christopherrbrown3/roanoke-star-tree-topper/pentagrammic_prism/previews/front.png

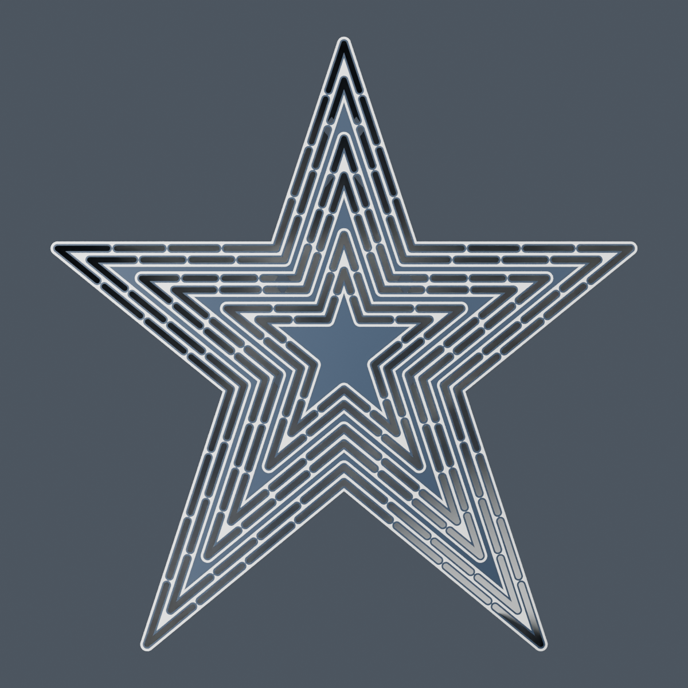
pentagrammic_prism/previews/front.png
