christopherrbrown3/roanoke-star-tree-topper/pentagrammic_prism/previews/rear.png

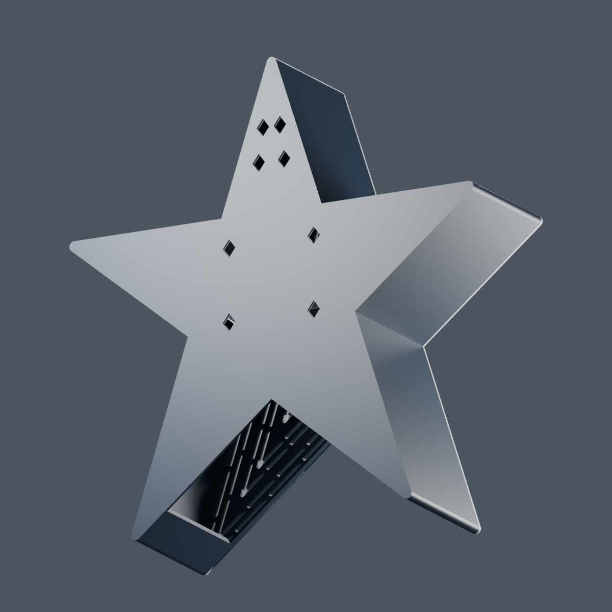
pentagrammic_prism/previews/rear.png
