christopherrbrown3/roanoke-star-tree-topper/print_in_place/body_material.stl

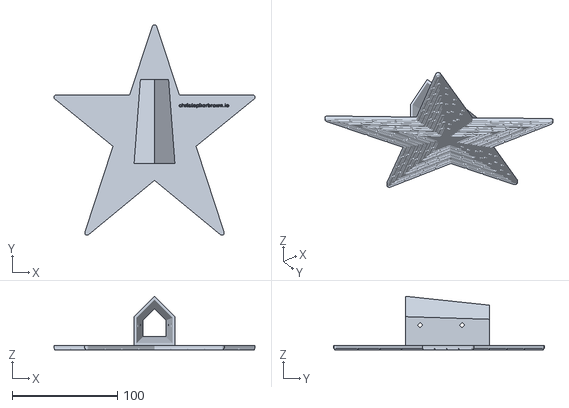
[picture p39: CAD file, 2026-09-19]
print_in_place/body_material.stl
191.0 x 200.0 x 50.8
