christopherrbrown3/roanoke-star-tree-topper/snap_back_prism/connector_fit_v2/construction/two_dot_wall.stl

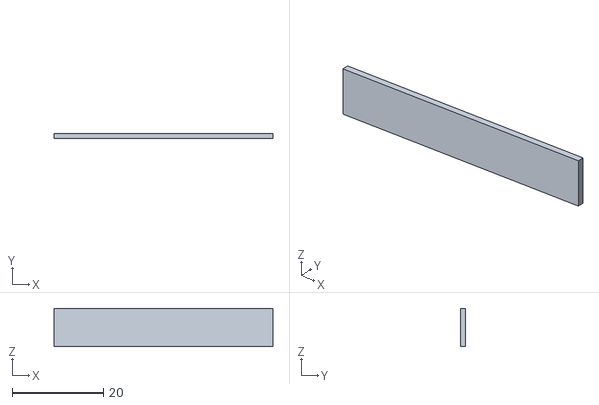
[picture p40: CAD file, 2026-10-10]
snap_back_prism/connector_fit_v2/construction/two_dot_wall.stl
48.0 x 1.20 x 8.40
