christopherrbrown3/roanoke-star-tree-topper/snap_back_prism/connector_fit_v2/two_dot_back.stl

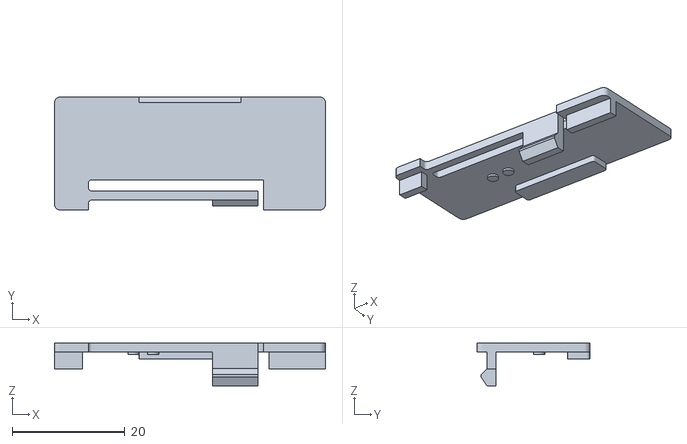
[picture p41: CAD file, 2026-10-10]
snap_back_prism/connector_fit_v2/two_dot_back.stl
48.0 x 20.0 x 7.60
