christopherrbrown3/roanoke-star-tree-topper/snap_back_prism/connector_sample_A1.3mf

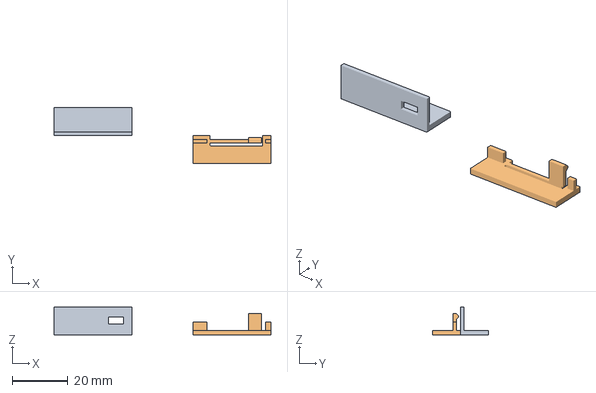
[picture p42: CAD file, 2026-10-10]
snap_back_prism/connector_sample_A1.3mf
78.0 x 20.0 x 9.90 mm
Snap connector sample x 2
