christopherrbrown3/roanoke-star-tree-topper/snap_back_prism/construction/hook_2.stl

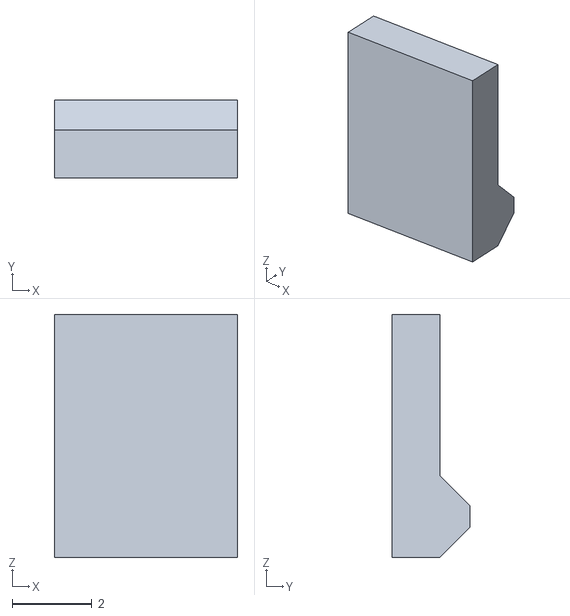
[picture p43: CAD file, 2026-10-10]
snap_back_prism/construction/hook_2.stl
4.60 x 1.95 x 6.10
