christopherrbrown3/roanoke-star-tree-topper/snap_back_prism/diffused/body_black.stl

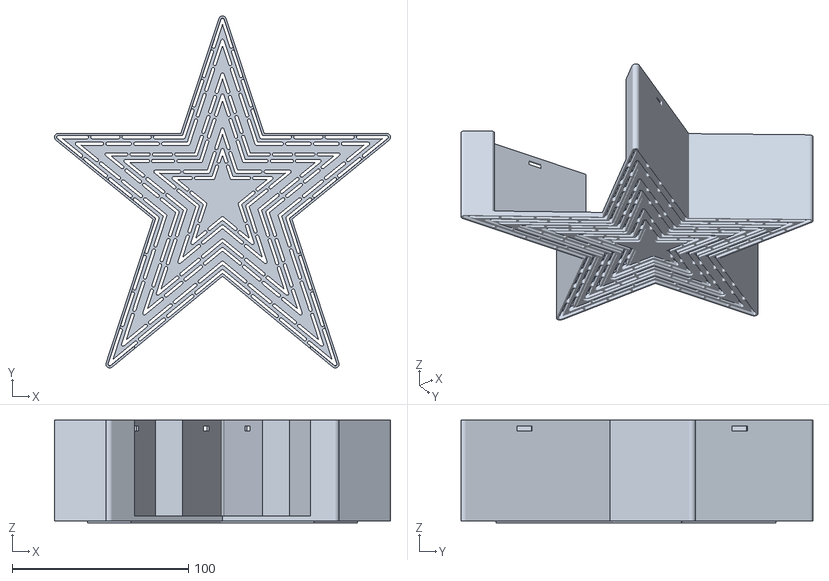
[picture p44: CAD file, 2026-10-10]
snap_back_prism/diffused/body_black.stl
191.0 x 200.0 x 58.4
