christopherrbrown3/roanoke-star-tree-topper/snap_back_prism/diffused/construction/white_upper_bands.stl

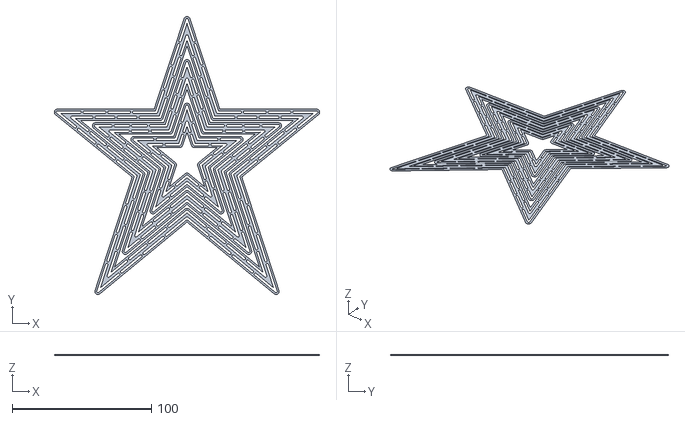
[picture p45: CAD file, 2026-10-10]
snap_back_prism/diffused/construction/white_upper_bands.stl
191.0 x 200.0 x 0.6
