christopherrbrown3/roanoke-star-tree-topper/snap_back_prism/two_dot/body_white_face.stl

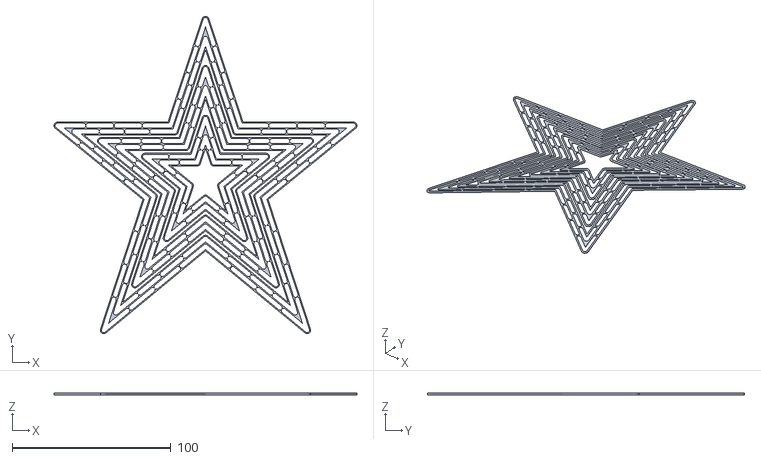
[picture p46: CAD file, 2026-10-10]
snap_back_prism/two_dot/body_white_face.stl
191.0 x 200.0 x 1.00
