christopherrbrown3/roanoke-star-tree-topper/snap_back_prism/two_dot/construction/hook_5.stl

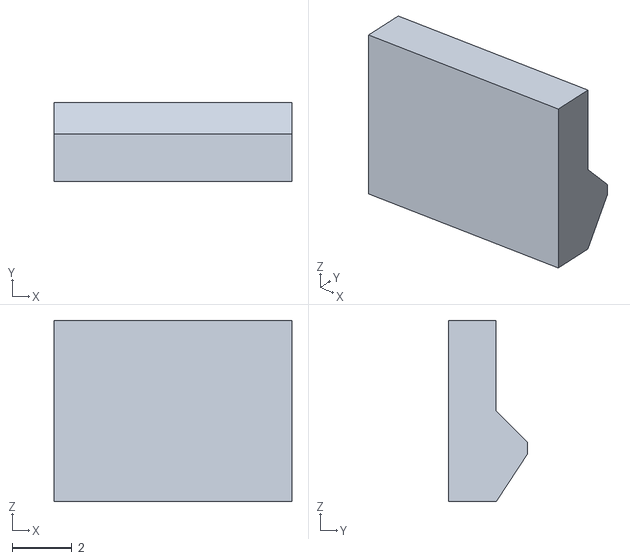
[picture p47: CAD file, 2026-10-10]
snap_back_prism/two_dot/construction/hook_5.stl
8.00 x 2.65 x 6.10
