christopherrbrown3/roanoke-star-tree-topper/pentagrammic_prism/roanoke_star_prism.stl

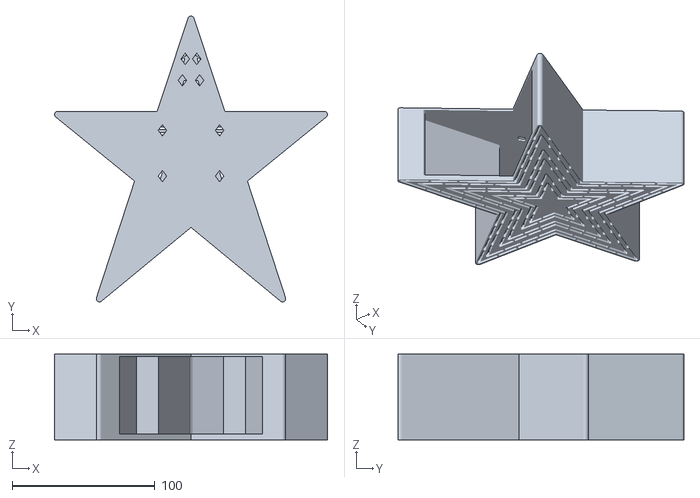
[picture p48: CAD file, 2026-10-10]
pentagrammic_prism/roanoke_star_prism.stl
191.0 x 200.0 x 60.0
