christopherrbrown3/roanoke-star-tree-topper/print_in_place/roanoke_star_A1_geometry_reference.stl

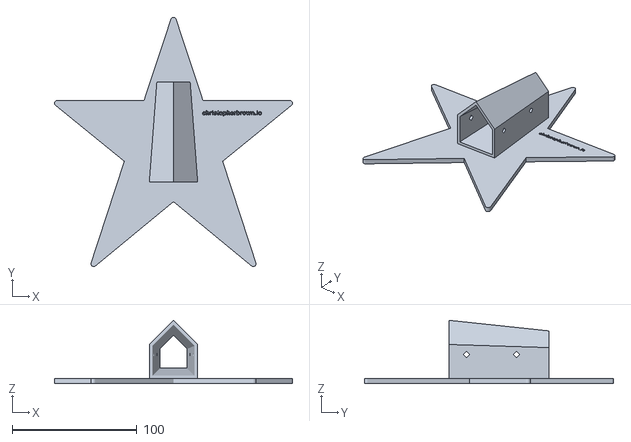
[picture p49: CAD file, 2026-09-19]
print_in_place/roanoke_star_A1_geometry_reference.stl
191.0 x 200.0 x 50.8
