christopherrbrown3/roanoke-star-tree-topper/snap_back_prism/construction/hook_1.stl

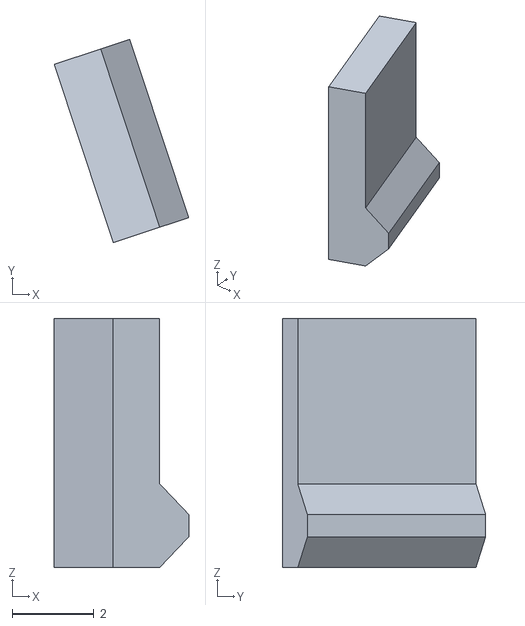
[picture p50: CAD file, 2026-10-10]
snap_back_prism/construction/hook_1.stl
3.30 x 4.98 x 6.10
