christopherrbrown3/roanoke-star-tree-topper/snap_back_prism/coupon_back.stl

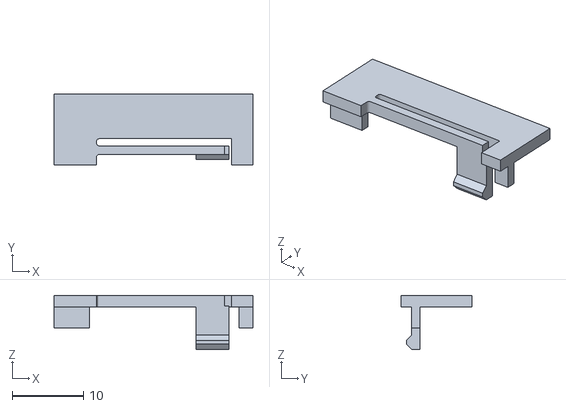
[picture p51: CAD file, 2026-10-10]
snap_back_prism/coupon_back.stl
28.0 x 10.0 x 7.60
