christopherrbrown3/roanoke-star-tree-topper/snap_back_prism/diffused/construction/continuous_white_face_region.stl

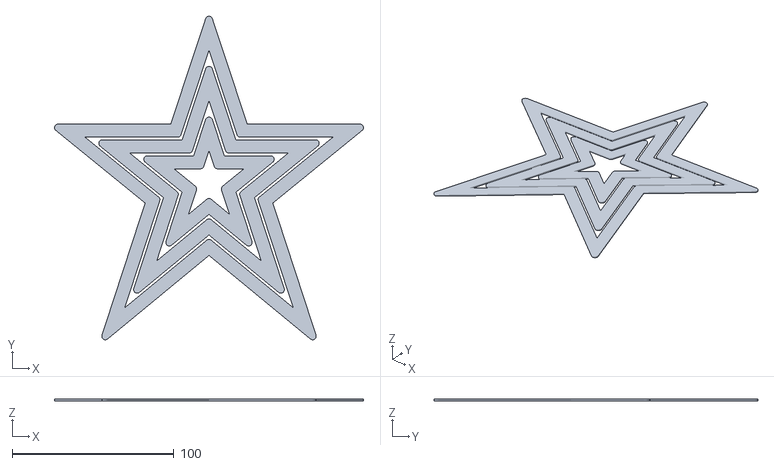
[picture p52: CAD file, 2026-10-10]
snap_back_prism/diffused/construction/continuous_white_face_region.stl
191.0 x 200.0 x 1.00
