christopherrbrown3/roanoke-star-tree-topper/snap_back_prism/spacing_v3/body_white_diffused.stl

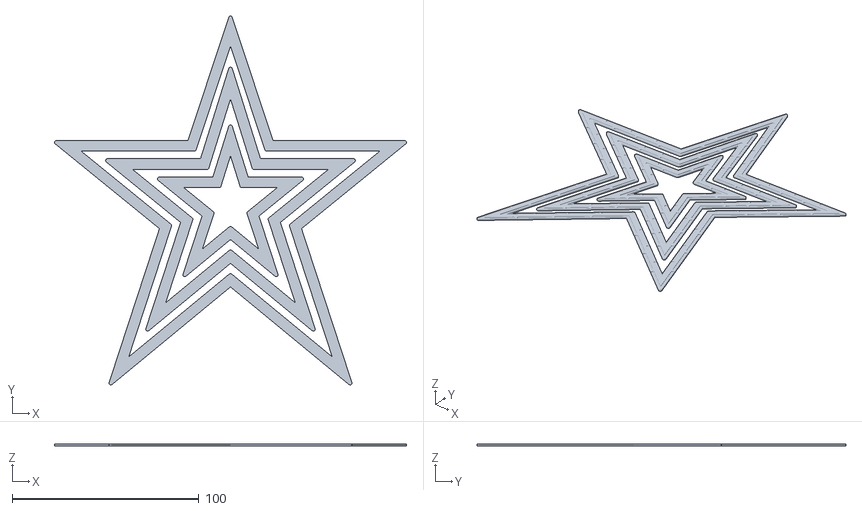
[picture p53: CAD file, 2026-10-10]
snap_back_prism/spacing_v3/body_white_diffused.stl
188.6 x 197.6 x 1.00
