christopherrbrown3/roanoke-star-tree-topper/snap_back_prism/two_dot/construction/lid_blank.stl

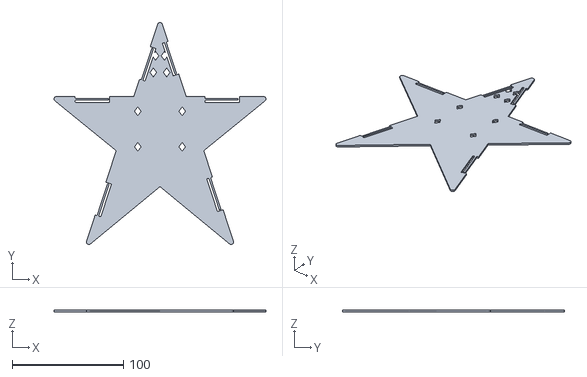
[picture p54: CAD file, 2026-10-10]
snap_back_prism/two_dot/construction/lid_blank.stl
191.0 x 200.0 x 1.60
