christopherrbrown3/roanoke-star-tree-topper/pentagrammic_prism/construction/bottom_mouth.stl

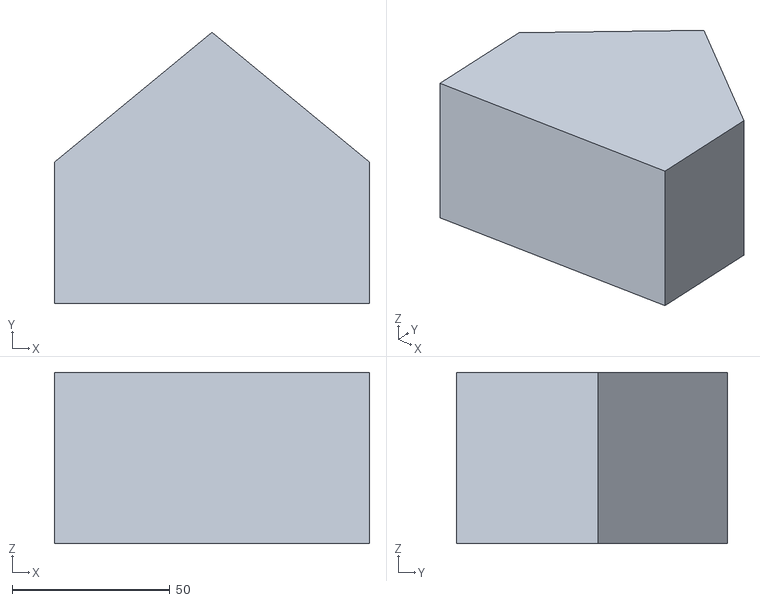
[picture p55: CAD file, 2026-10-10]
pentagrammic_prism/construction/bottom_mouth.stl
100.0 x 86.1 x 54.4
