christopherrbrown3/roanoke-star-tree-topper/pentagrammic_prism/dark_shell.stl

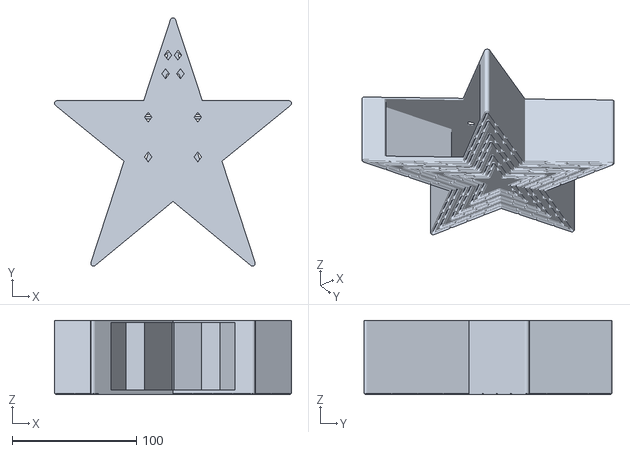
[picture p56: CAD file, 2026-10-10]
pentagrammic_prism/dark_shell.stl
191.0 x 200.0 x 60.0
