christopherrbrown3/roanoke-star-tree-topper/print_in_place/white_tube_material.stl

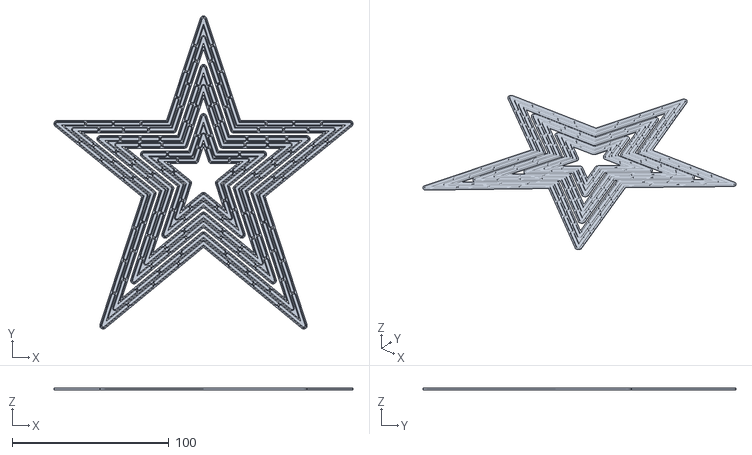
[picture p57: CAD file, 2026-09-19]
print_in_place/white_tube_material.stl
191.0 x 200.0 x 1.00
