christopherrbrown3/roanoke-star-tree-topper/snap_back_prism/connector_fit_v2/connector_fit_v2_A1.3mf

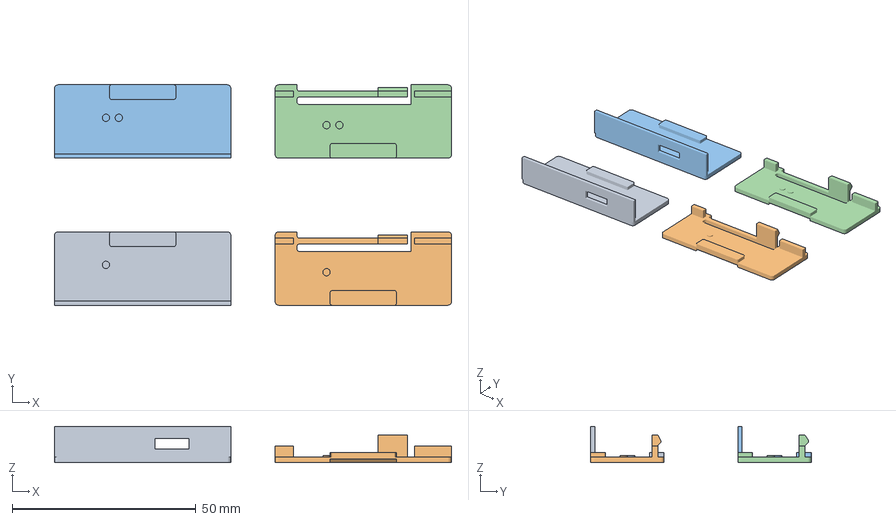
[picture p58: CAD file, 2026-10-10]
snap_back_prism/connector_fit_v2/connector_fit_v2_A1.3mf
108.0 x 60.0 x 9.90 mm
Connector fit v2 - one and two dots x 4
