christopherrbrown3/roanoke-star-tree-topper/snap_back_prism/connector_fit_v2/construction/two_dot_floor.stl

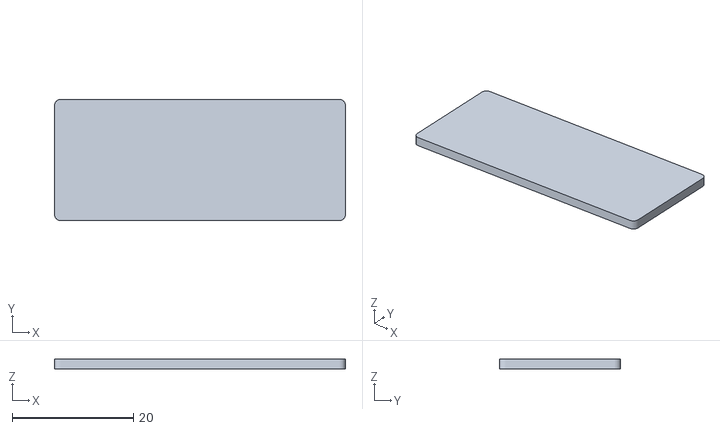
[picture p59: CAD file, 2026-10-10]
snap_back_prism/connector_fit_v2/construction/two_dot_floor.stl
48.0 x 20.0 x 1.60
