christopherrbrown3/roanoke-star-tree-topper/snap_back_prism/construction/coupon_rim.stl

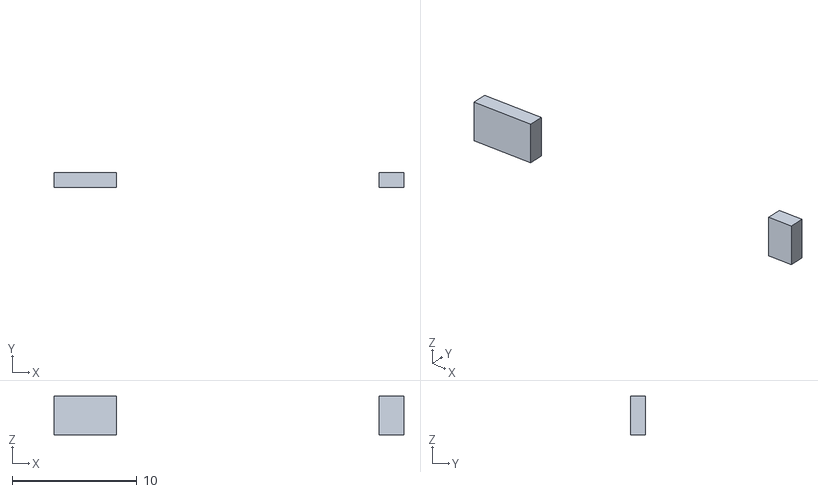
[picture p60: CAD file, 2026-10-10]
snap_back_prism/construction/coupon_rim.stl
28.0 x 1.20 x 3.10
