christopherrbrown3/roanoke-star-tree-topper/snap_back_prism/diffused/construction/white_skin_and_bands.stl

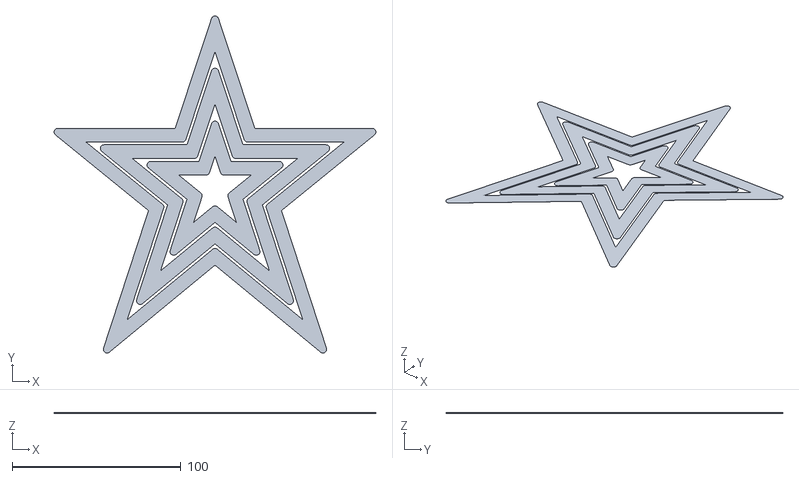
[picture p61: CAD file, 2026-10-10]
snap_back_prism/diffused/construction/white_skin_and_bands.stl
191.0 x 200.0 x 0.4
