christopherrbrown3/roanoke-star-tree-topper/snap_back_prism/diffused/test_white.stl

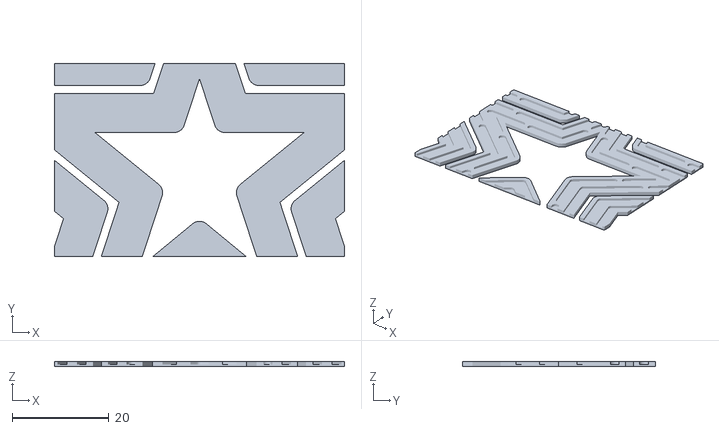
[picture p62: CAD file, 2026-10-10]
snap_back_prism/diffused/test_white.stl
60.0 x 40.0 x 1.00
