christopherrbrown3/roanoke-star-tree-topper/pentagrammic_prism/construction/inner_cavity.stl

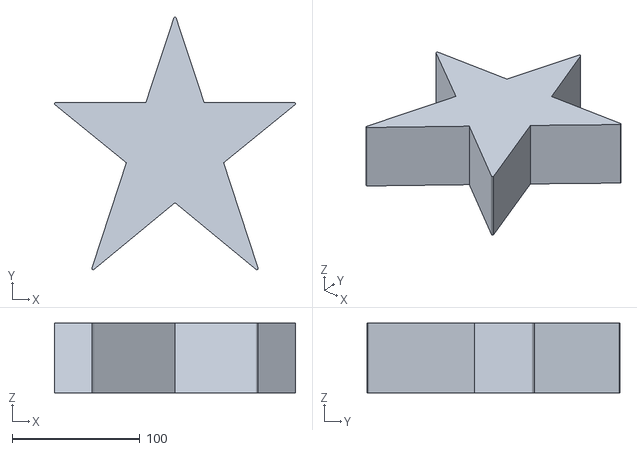
[picture p63: CAD file, 2026-10-10]
pentagrammic_prism/construction/inner_cavity.stl
188.6 x 197.6 x 54.4
