christopherrbrown3/roanoke-star-tree-topper/pentagrammic_prism/roanoke_star_prism_A1_single_color.3mf

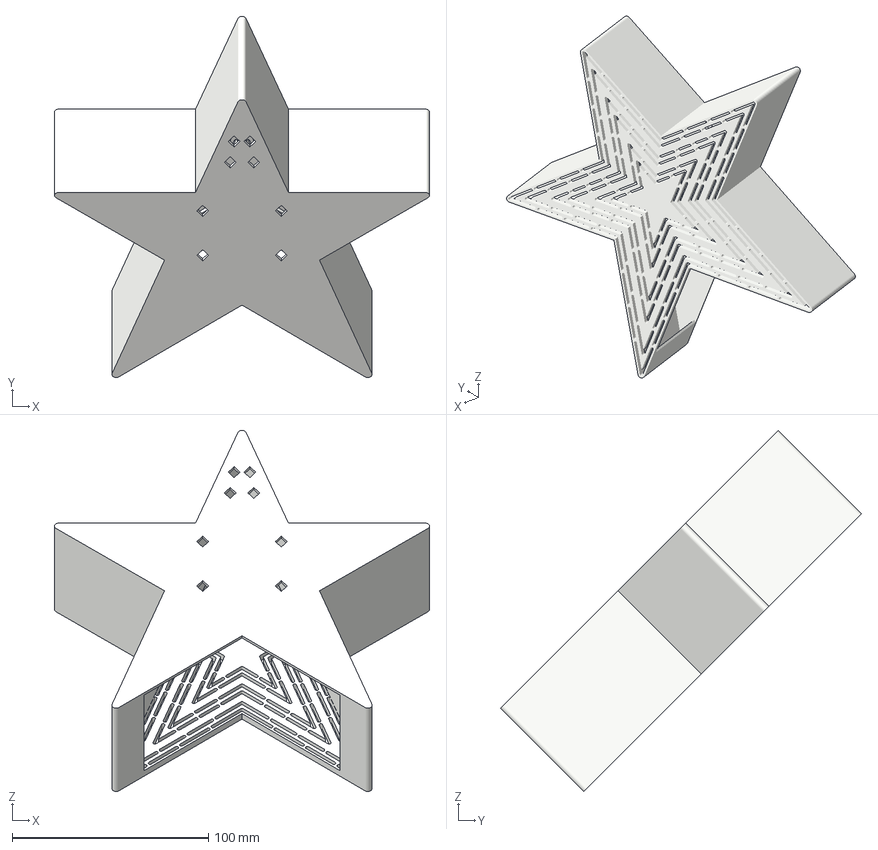
[picture p64: CAD file, 2026-10-10]
pentagrammic_prism/roanoke_star_prism_A1_single_color.3mf
191.0 x 183.8 x 183.8 mm
