christopherrbrown3/roanoke-star-tree-topper/snap_back_prism/connector_fit_v2/construction/two_dot_floor_grip.stl

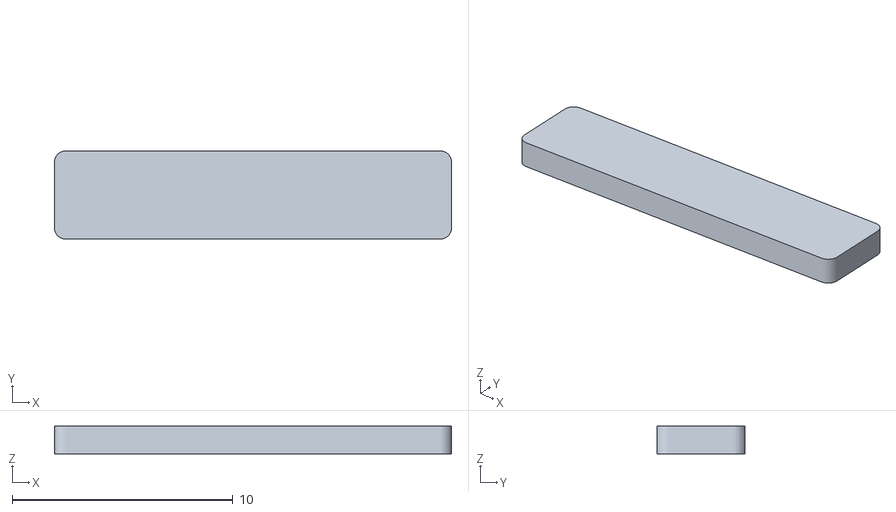
[picture p65: CAD file, 2026-10-10]
snap_back_prism/connector_fit_v2/construction/two_dot_floor_grip.stl
18.0 x 4.00 x 1.25
