christopherrbrown3/roanoke-star-tree-topper/snap_back_prism/construction/bottom_mouth.stl

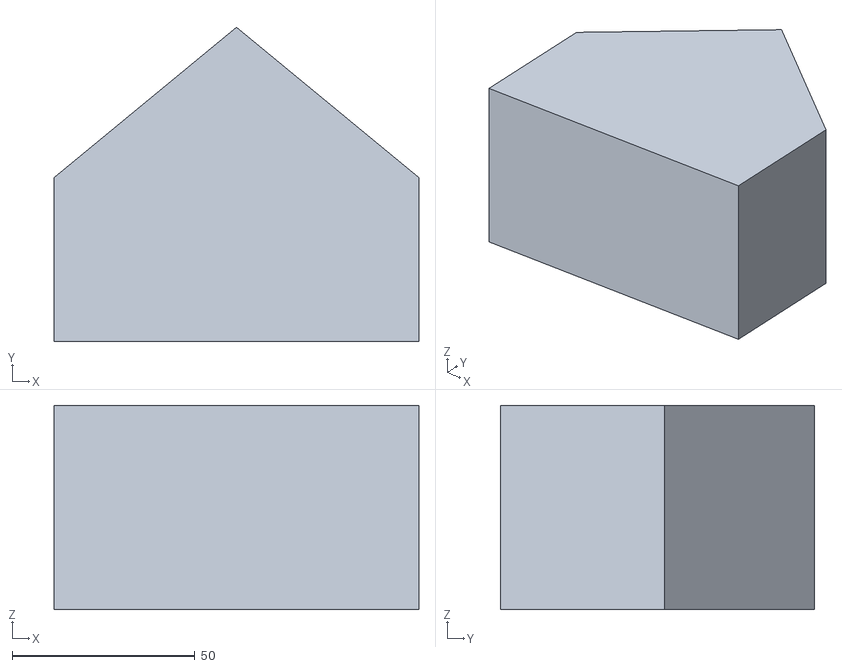
[picture p66: CAD file, 2026-10-10]
snap_back_prism/construction/bottom_mouth.stl
100.0 x 86.1 x 56.0
