christopherrbrown3/roanoke-star-tree-topper/snap_back_prism/diffused/construction/sample_crop.stl

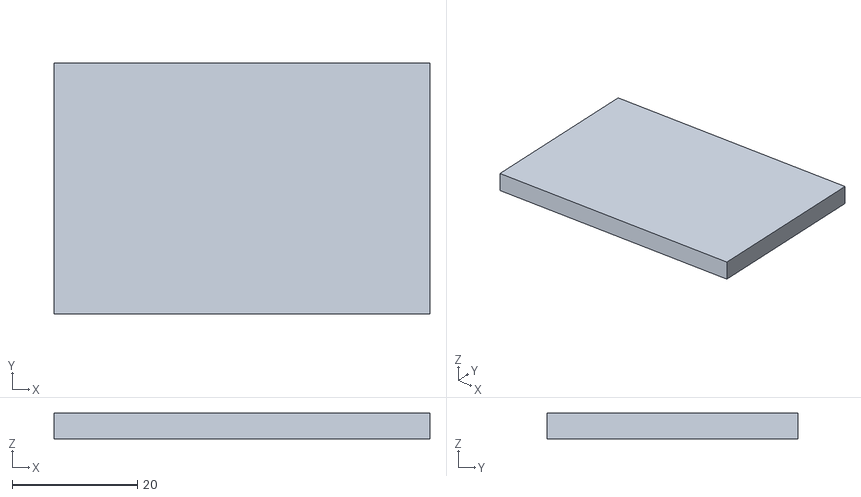
[picture p67: CAD file, 2026-10-10]
snap_back_prism/diffused/construction/sample_crop.stl
60.0 x 40.0 x 4.10
