christopherrbrown3/roanoke-star-tree-topper/snap_back_prism/diffused/test_black.stl

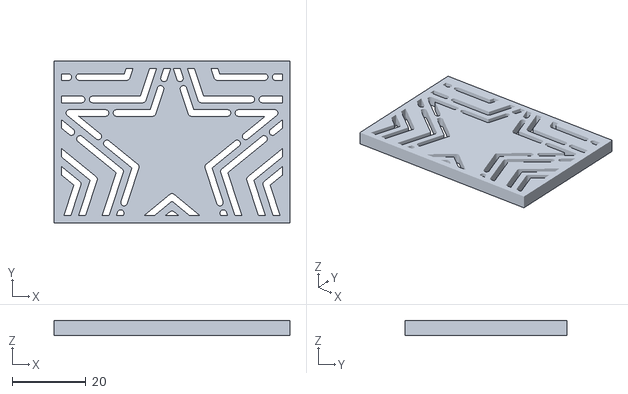
[picture p68: CAD file, 2026-10-10]
snap_back_prism/diffused/test_black.stl
64.0 x 44.0 x 4.00
