christopherrbrown3/roanoke-star-tree-topper/snap_back_prism/two_dot/construction/locating_rim.stl

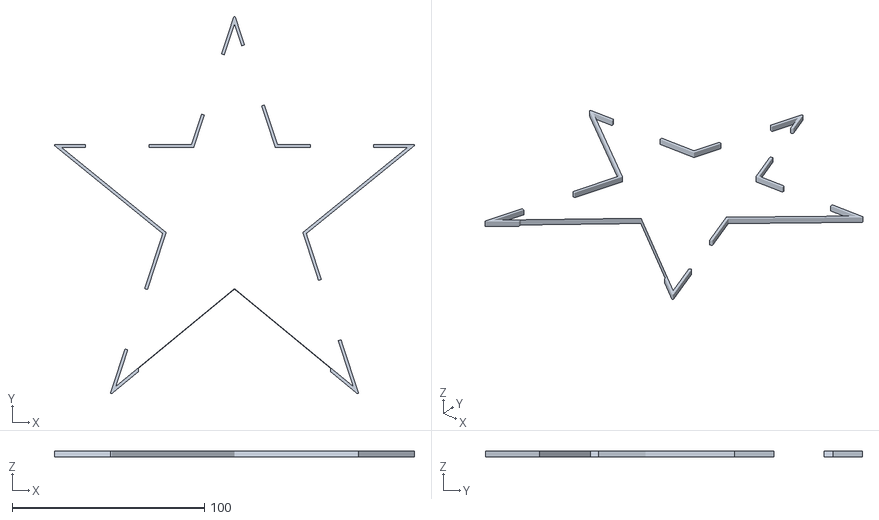
[picture p69: CAD file, 2026-10-10]
snap_back_prism/two_dot/construction/locating_rim.stl
187.5 x 196.5 x 3.10
