christopherrbrown3/roanoke-star-tree-topper/snap_back_prism/connector_fit_v2/construction/one_dot_cap_bevel.stl

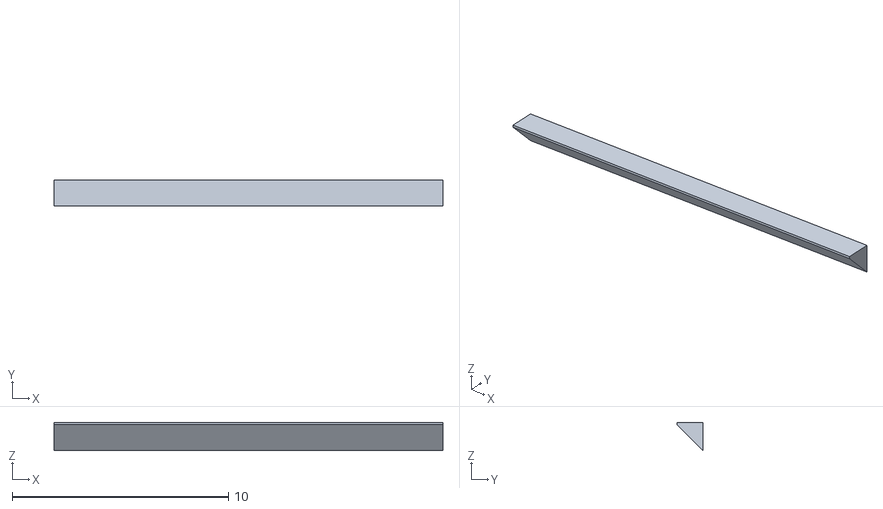
[picture p70: CAD file, 2026-10-10]
snap_back_prism/connector_fit_v2/construction/one_dot_cap_bevel.stl
18.0 x 1.20 x 1.30
