christopherrbrown3/roanoke-star-tree-topper/snap_back_prism/construction/coupon_wall.stl

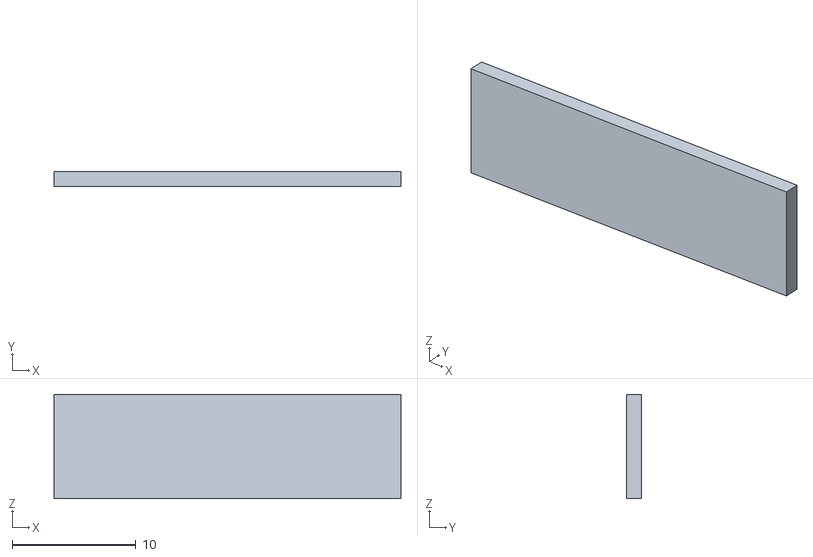
[picture p71: CAD file, 2026-10-10]
snap_back_prism/construction/coupon_wall.stl
28.0 x 1.20 x 8.40
