christopherrbrown3/roanoke-star-tree-topper/snap_back_prism/coupon_catch.stl

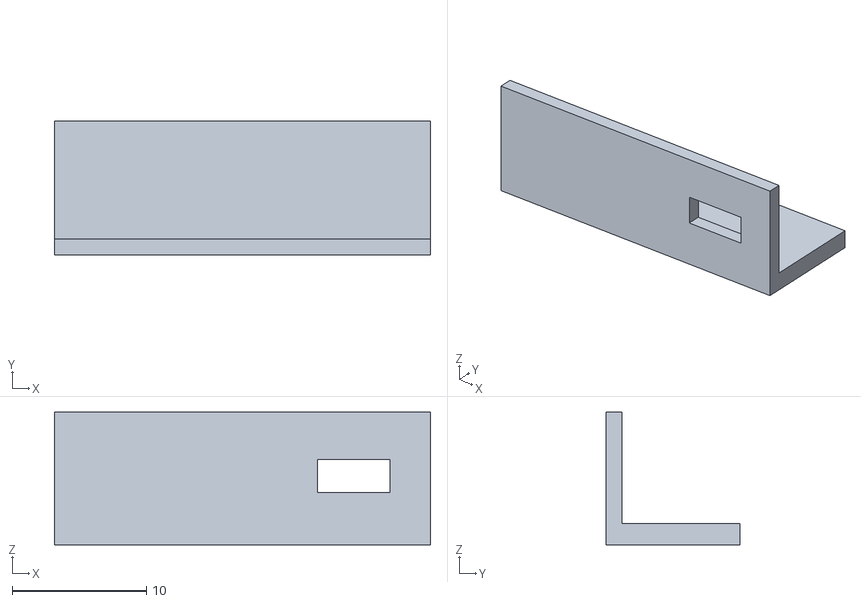
[picture p72: CAD file, 2026-10-10]
snap_back_prism/coupon_catch.stl
28.0 x 10.0 x 9.90
