christopherrbrown3/roanoke-star-tree-topper/snap_back_prism/diffused/diffuser_test_A1.3mf

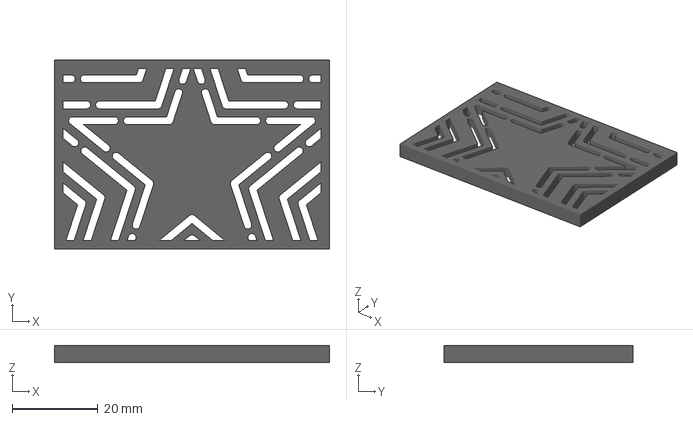
[picture p73: CAD file, 2026-10-10]
snap_back_prism/diffused/diffuser_test_A1.3mf
64.0 x 44.0 x 4.00 mm
