christopherrbrown3/roanoke-star-tree-topper/snap_back_prism/two_dot/construction/builder_mark_cutter.stl

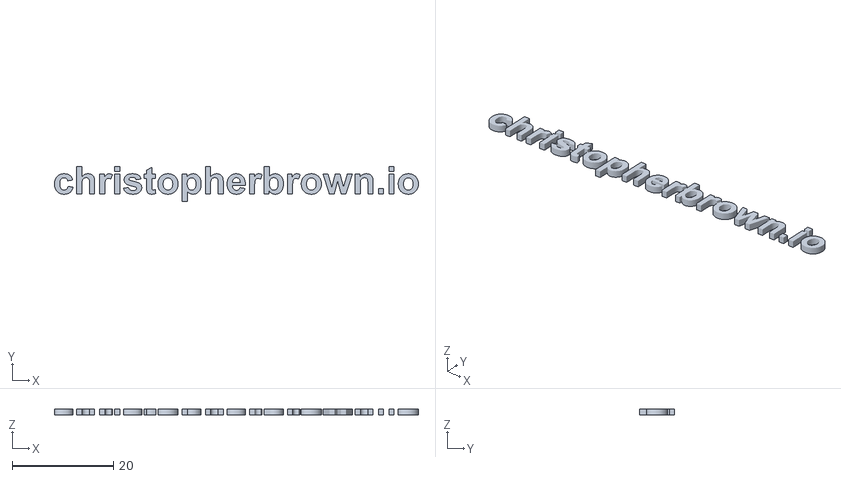
[picture p74: CAD file, 2026-10-10]
snap_back_prism/two_dot/construction/builder_mark_cutter.stl
72.0 x 6.86 x 1.20
