christopherrbrown3/roanoke-star-tree-topper/snap_back_prism/two_dot/construction/hook_6.stl

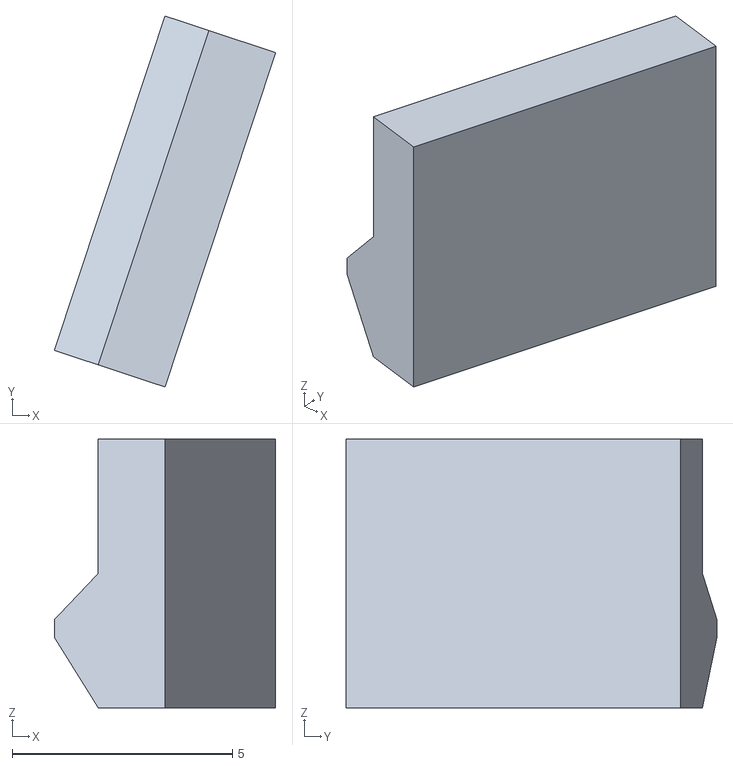
[picture p75: CAD file, 2026-10-10]
snap_back_prism/two_dot/construction/hook_6.stl
5.03 x 8.43 x 6.10
