christopherrbrown3/roanoke-star-tree-topper/pentagrammic_prism/construction/tree_leader_clearance_reference.stl

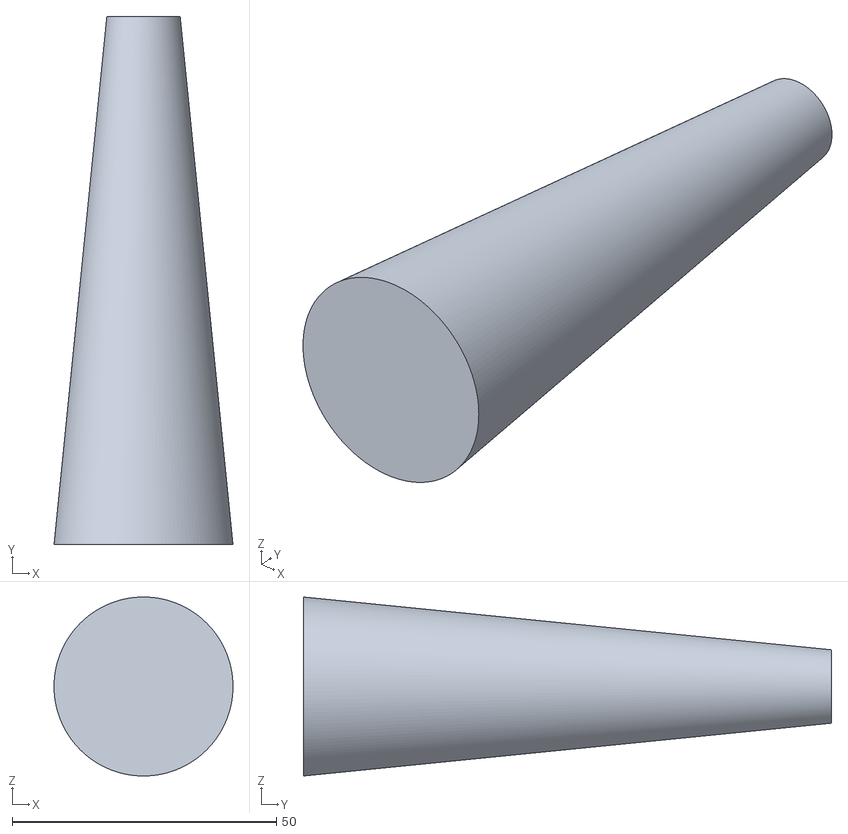
[picture p76: CAD file, 2026-10-10]
pentagrammic_prism/construction/tree_leader_clearance_reference.stl
33.9 x 100.0 x 33.9
