christopherrbrown3/roanoke-star-tree-topper/snap_back_prism/connector_fit_v2/construction/one_dot_window.stl

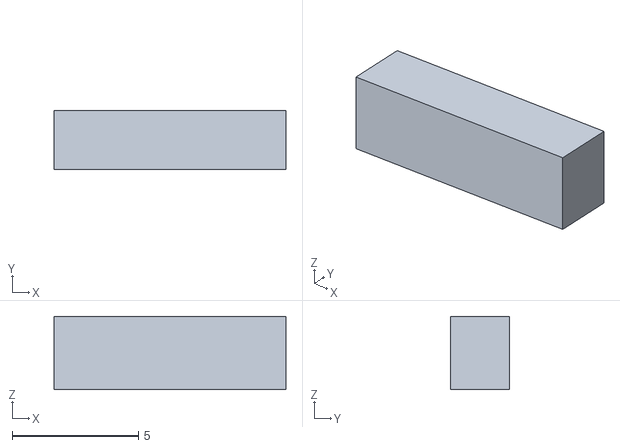
[picture p77: CAD file, 2026-10-10]
snap_back_prism/connector_fit_v2/construction/one_dot_window.stl
9.20 x 2.35 x 2.90
