christopherrbrown3/roanoke-star-tree-topper/pentagrammic_prism/construction/outline.stl

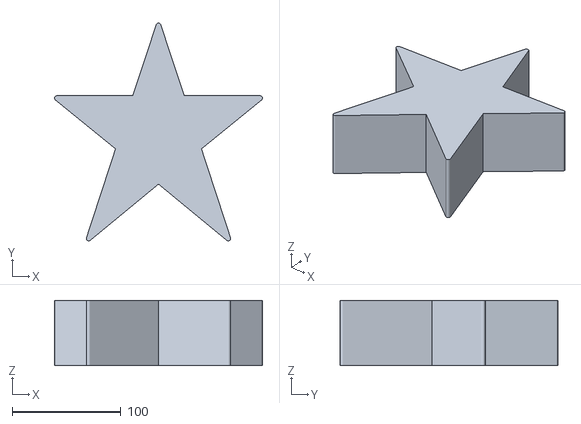
[picture p78: CAD file, 2026-10-10]
pentagrammic_prism/construction/outline.stl
191.0 x 200.0 x 60.0
