christopherrbrown3/roanoke-star-tree-topper/snap_back_prism/connector_fit_v2/construction/two_dot_cap_dots.stl

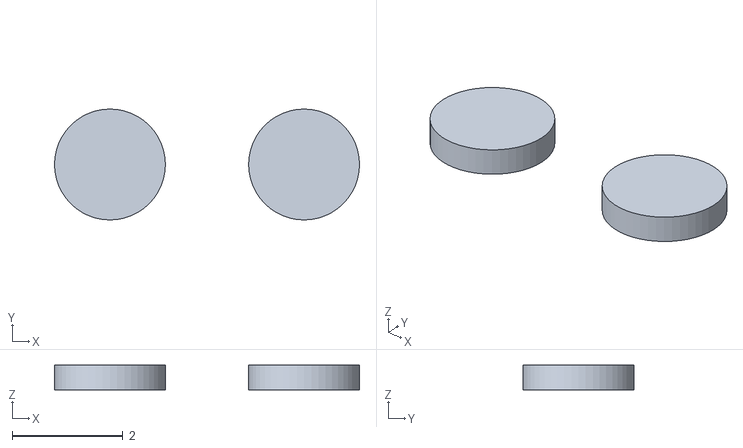
[picture p79: CAD file, 2026-10-10]
snap_back_prism/connector_fit_v2/construction/two_dot_cap_dots.stl
5.50 x 2.00 x 0.45
