christopherrbrown3/roanoke-star-tree-topper/snap_back_prism/construction/body_blank.stl

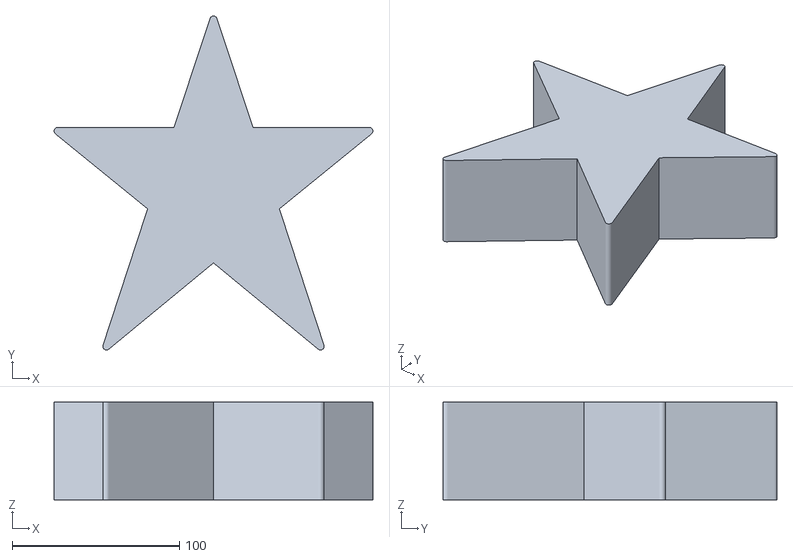
[picture p80: CAD file, 2026-10-10]
snap_back_prism/construction/body_blank.stl
191.0 x 200.0 x 58.4
