christopherrbrown3/roanoke-star-tree-topper/pentagrammic_prism/construction/rear_vents.stl

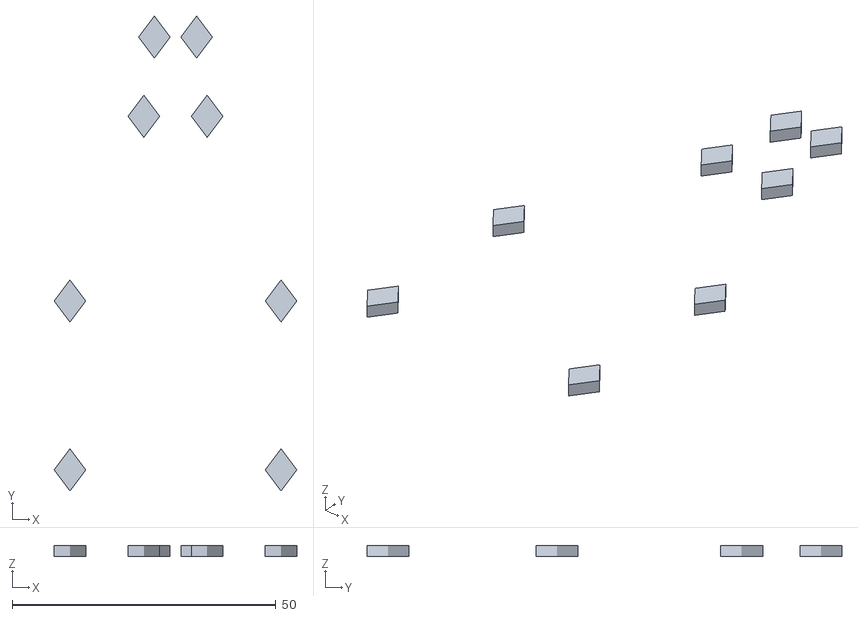
[picture p81: CAD file, 2026-10-10]
pentagrammic_prism/construction/rear_vents.stl
46.0 x 90.0 x 2.00
