christopherrbrown3/roanoke-star-tree-topper/snap_back_prism/connector_fit_v2/construction/one_dot_cap.stl

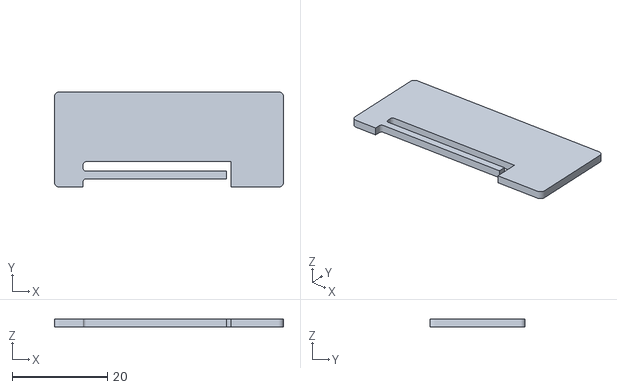
[picture p82: CAD file, 2026-10-10]
snap_back_prism/connector_fit_v2/construction/one_dot_cap.stl
48.0 x 20.0 x 1.60
