christopherrbrown3/roanoke-star-tree-topper/snap_back_prism/two_dot/construction/open_cavity.stl

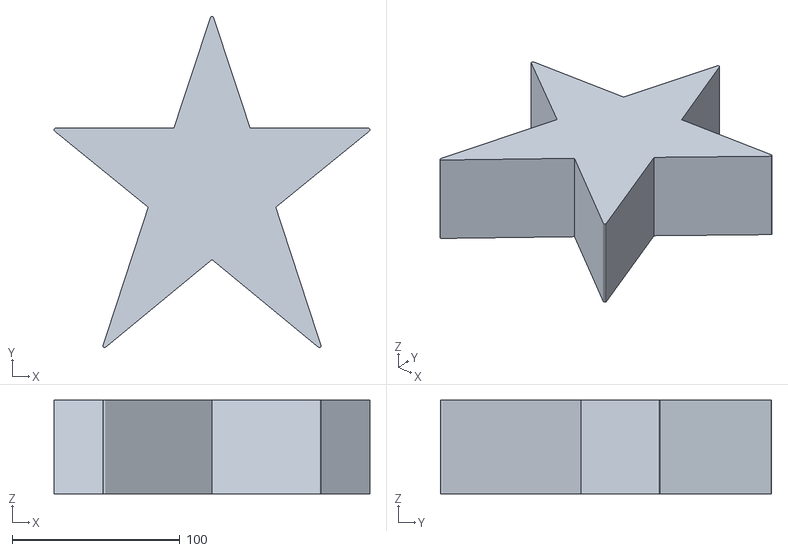
[picture p83: CAD file, 2026-10-10]
snap_back_prism/two_dot/construction/open_cavity.stl
188.6 x 197.6 x 56.0
