christopherrbrown3/roanoke-star-tree-topper/snap_back_prism/connector_fit_v2/construction/one_dot_hook.stl

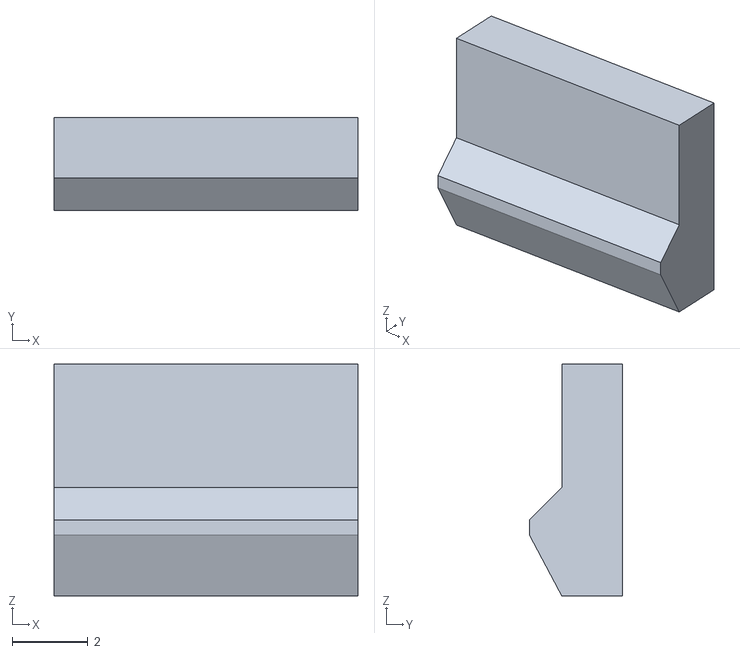
[picture p84: CAD file, 2026-10-10]
snap_back_prism/connector_fit_v2/construction/one_dot_hook.stl
8.00 x 2.45 x 6.10
