christopherrbrown3/roanoke-star-tree-topper/snap_back_prism/construction/coupon_floor.stl

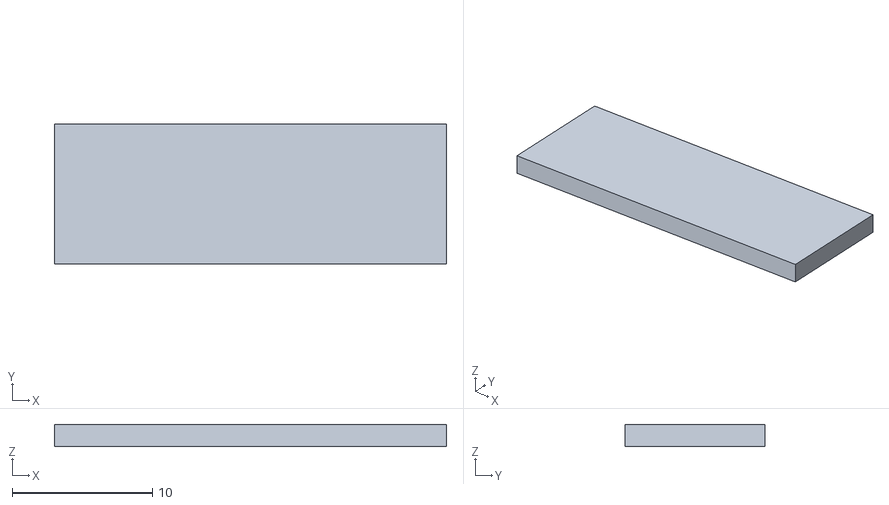
[picture p85: CAD file, 2026-10-10]
snap_back_prism/construction/coupon_floor.stl
28.0 x 10.0 x 1.60
