christopherrbrown3/roanoke-star-tree-topper/snap_back_prism/connector_fit_v2/construction/one_dot_cap_dots.stl

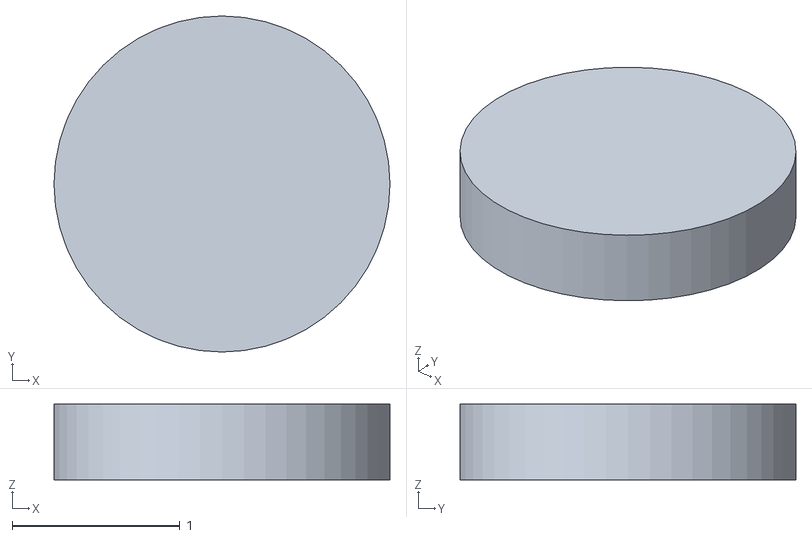
[picture p86: CAD file, 2026-10-10]
snap_back_prism/connector_fit_v2/construction/one_dot_cap_dots.stl
2.00 x 2.00 x 0.45
