christopherrbrown3/roanoke-star-tree-topper/snap_back_prism/construction/catch_windows.stl

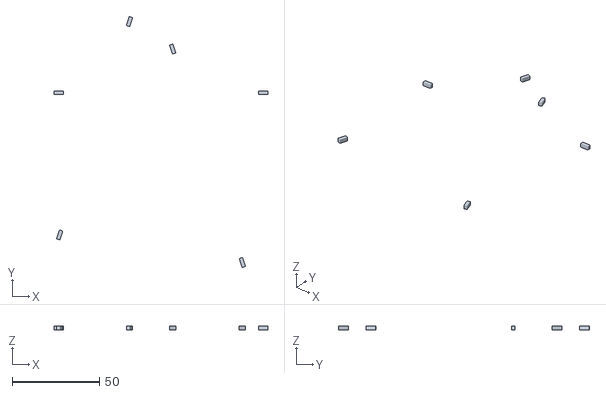
[picture p87: CAD file, 2026-10-10]
snap_back_prism/construction/catch_windows.stl
122.3 x 143.7 x 2.45
