christopherrbrown3/roanoke-star-tree-topper/snap_back_prism/construction/coupon_window.stl

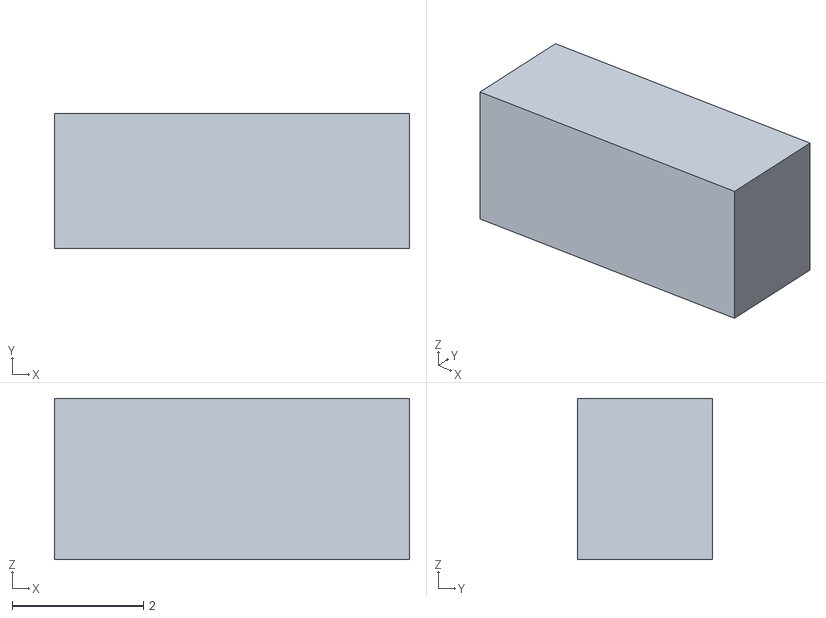
[picture p88: CAD file, 2026-10-10]
snap_back_prism/construction/coupon_window.stl
5.40 x 2.05 x 2.45
