christopherrbrown3/roanoke-star-tree-topper/snap_back_prism/construction/coupon_lid.stl

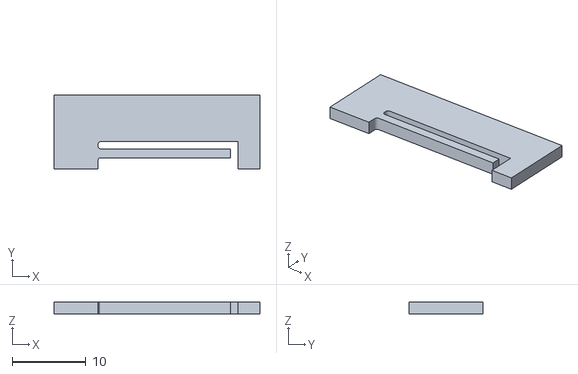
[picture p89: CAD file, 2026-10-10]
snap_back_prism/construction/coupon_lid.stl
28.0 x 10.0 x 1.60
