christopherrbrown3/roanoke-star-tree-topper/snap_back_prism/connector_fit_v2/construction/two_dot_hook.stl

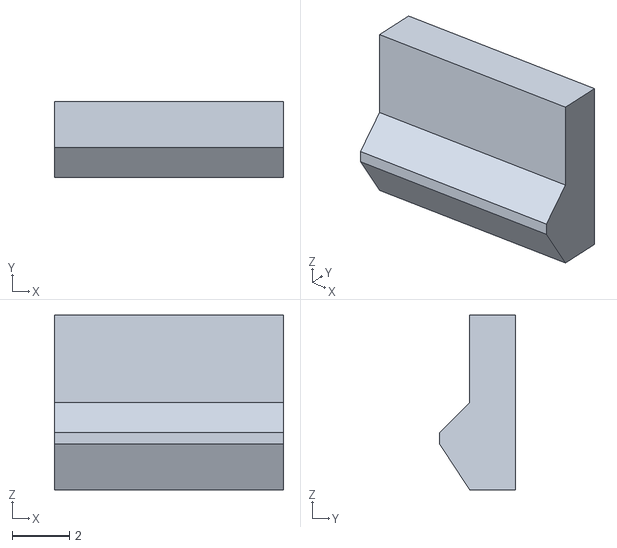
[picture p90: CAD file, 2026-10-10]
snap_back_prism/connector_fit_v2/construction/two_dot_hook.stl
8.00 x 2.65 x 6.10
